jonthomasson/retroii/retroii-case/Apple_II_europlus_side.jpg

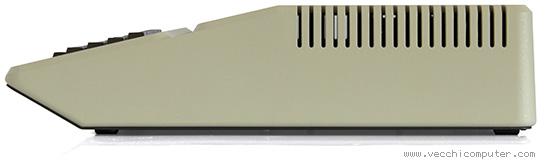
retroii-case/Apple_II_europlus_side.jpg
