jonthomasson/retroii/retroii-case/audio_cassette.png

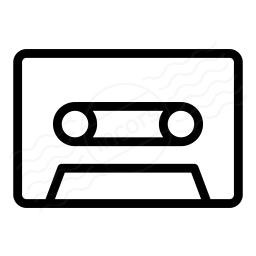
retroii-case/audio_cassette.png
