jonthomasson/retroii/retroii-case/choplft1.png

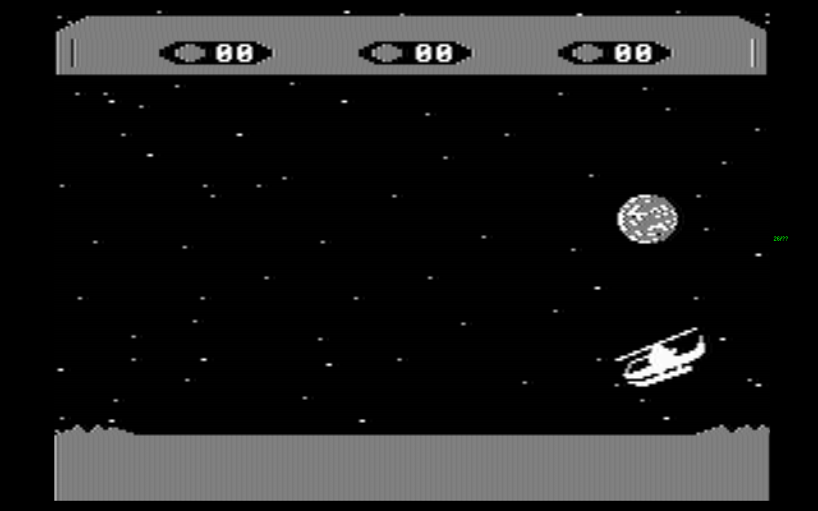
retroii-case/choplft1.png
