jonthomasson/retroii/retroii-case/headphones.png

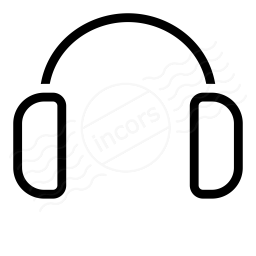
retroii-case/headphones.png
