jonthomasson/retroii/retroii-case/image81591.png

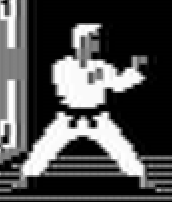
retroii-case/image81591.png
