jonthomasson/retroii/retroii-case/karateka.png

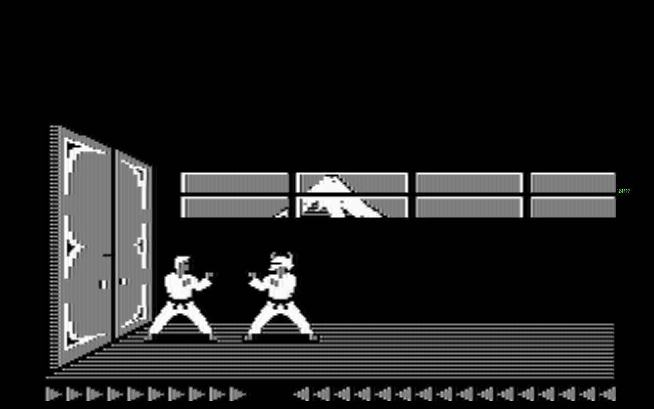
retroii-case/karateka.png
