jonthomasson/retroii/rev1.a/retroii/pics/kbd_latch.PNG

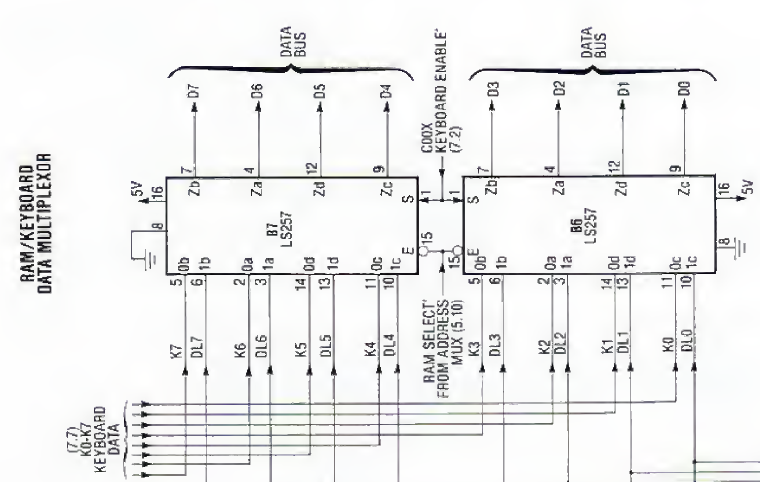
rev1.a/retroii/pics/kbd_latch.PNG
