jonthomasson/retroii/3d/D15S33E4GV00LFC.stp

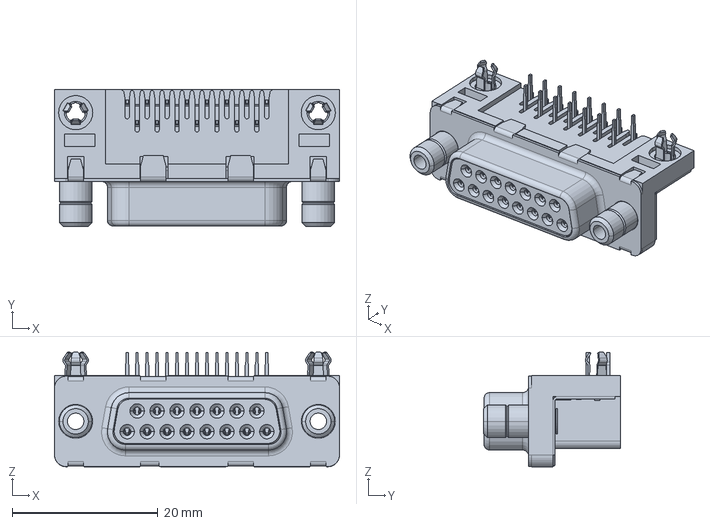
[picture p28: CAD file, 2019-04-12]
3d/D15S33E4GV00LFC.stp
39.1 x 18.8 x 15.8 mm
