jonthomasson/retroii/3d/CONN_5747844-6.step

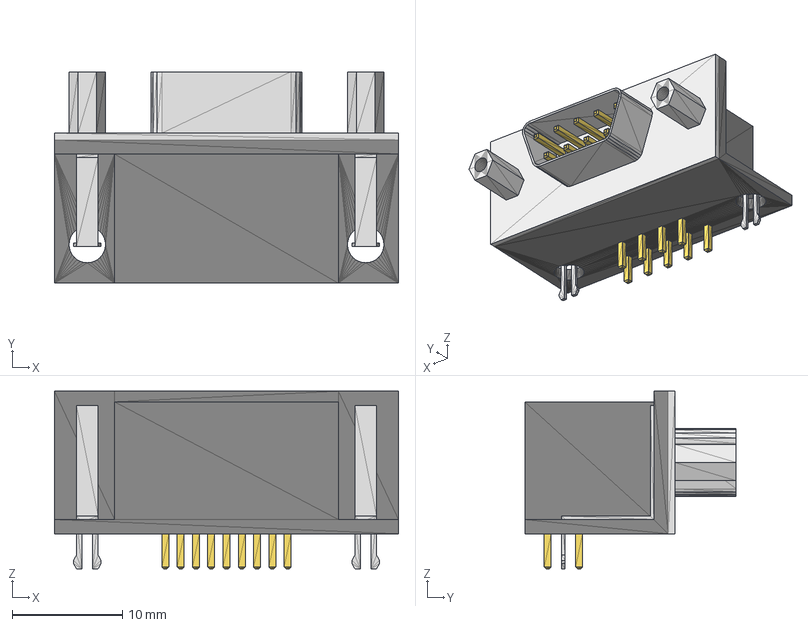
[picture p29: CAD file, 2019-04-12]
3d/CONN_5747844-6.step
31.2 x 19.2 x 16.1 mm
