jonthomasson/retroii/firmware/retroii/video/r2_video.spin

''------------------------------------------------------------------------------------------------
'' RETRO ][ video driver
''
'' Copyright (c) 2020 Jon Thomasson
''
''------------------------------------------------------------------------------------------------

'' This version uses two cogs, one for the VGA output, and one for routines that draw
'' on the bitmap.
''------------------------------------------------------------------------------------------------
'' Video Circuit:
''
'' Pin              VGA
'' Group   240Ω
''  +0 ──────── 14 Vertical Sync                +5V ──── 9
''         240Ω
''  +1 ──────── 13 Horizontal Sync              GND ┳─── 5
''         470Ω                                          │
''  +2 ──────┳─ 3  Blue                              ┣─── 6
''         240Ω │                                        │
''  +3 ──────┘                                        ┣─── 7
''         470Ω                                          │
''  +4 ──────┳─ 2  Green                             ┣─── 8
''         240Ω │                                        │
''  +5 ──────┘                                        └─── 10
''         470Ω                                         
''  +6 ──────┳─ 1  Red
''         240Ω │
''  +7 ──────┘
''------------------------------------------------------------------------------------------------

CON

  '288x240 resolution
  WIDTH  = 288 '288
  HEIGHT = 240
  FREQ_VALUE = 608207634 '304103817 '304104364
  CTRA_VALUE = %0_00001_011 '%0_00001_100
  FP = 7 '7
  SP = 43'43
  BP = 22'22

  'Color value constants
  #$04, BLUE, #$08, GREEN
  #$10, RED, #$0C, LT_BLUE
  #$18, YELLOW, #$14, LT_RED
  #$00, BLACK, #$1C, WHITE 
  #$FF, FULL 'full 6 color pallet mode

  PC_FP  = WIDTH + FP
  BLKS   = 480 / HEIGHT         'Number of times to repeat each video line

  COLS   = WIDTH / 8            'Width of screen in characters
  ROWS   = HEIGHT / 8           'Height of screen in characters
  MAX_C  = COLS - 1             'Maximum column
  MAX_R  = ROWS - 1             'Maximum row

  PSIZE  = WIDTH * HEIGHT       'Total number of pixels
  LSIZE  = PSIZE / 32           'Size of screen buffer in longs
  LPROW  = 10 'COLS / 4             'Longs per screen line

  MAX_X  = WIDTH - 1            'Maximum value of x coordinate
  MAX_Y  = HEIGHT - 1           'Maximum value of y coordinate

  SCROFF = WIDTH                'Scroll offset
  SCRCNT = LSIZE - (SCROFF / 4) 'Scroll long count

  CMD_CHAR  = $00_00_00_00
  CMD_PIXEL = $04_00_00_00
  CMD_LORES = $10_00_00_00
  CMD_HIRES  = $20_00_00_00
  
  MODE_HIRES = 2
  MODE_TEXT = 1
  MODE_LORES = 3
  
  LBUFFER_SIZE = 2400           'Size of pixel buffer in longs (320*240/32) NOTE: this size accounts for the color bit.
  BUFFER_WIDTH = 320
  
VAR 
  byte  cursorx, cursory, cog1, cog2, cog3, reverse, cursor_state, mode_retroii, mode_retroii_old, ss_page2, ss_mix, update_vcfg, screen_mode, old_screen_mode
  long  pixel_bfr[LBUFFER_SIZE]
  long  pixel_colors, frame_count, cursor_pos, cursor_mask, hires_busy, draw_command, hires_command, debug_val, display_debug, current_clock
  long  frame_count_hires', ram_lock                        
  'long  group1_colors, group2_colors 'color paletts. 

PUB Char(c) | idx, ptr, tmp
'------------------------------------------------------------------------------------------------
'' Print a character on the screen, then advance the cursor.
''
'' c - Character to print.
'------------------------------------------------------------------------------------------------
  c &= 255
  
  'If a printable character
  if c > 31
    repeat while draw_command <> 0
    draw_command := c | (cursorx << 8) | (cursory << 17)
    cursorx += 1
 
  'UpdateCursor

PUB RChar(c)
'------------------------------------------------------------------------------------------------
'' Print a character on the screen, in reverse video, then advance the cursor.
''
'' c - Character to print.
'------------------------------------------------------------------------------------------------
  reverse := 255
  Char(c)
  reverse := 0

PUB LowRes(c, x, y) 
'------------------------------------------------------------------------------------------------
'' Plots a lores byte of data on the screen.
''
'' c - data byte.
'' x - The X coordinate.
'' y - The Y coordinate.
'------------------------------------------------------------------------------------------------
  repeat while draw_command <> 0
  draw_command := c | (x << 8) | (y << 17) | CMD_LORES


PUB Str(s) | b
'------------------------------------------------------------------------------------------------
'' Write a NULL terminated string starting at the current cursor position.
''
'' s - Address of a Null terminated string.
'------------------------------------------------------------------------------------------------
  repeat
    b := byte[s]
    if b == 0
      return
    Char(b)
    s += 1

PUB Pos(X, Y)
'------------------------------------------------------------------------------------------------
'' Set the XY position of the character cursor.
'------------------------------------------------------------------------------------------------
  cursorx := X
  cursory := Y
  'cursorx := (X <# MAX_C) #> 0 
  'cursory := (Y <# MAX_R) #> 0 
  'UpdateCursor

PUB GetX
'------------------------------------------------------------------------------------------------
'' Returns the x cursor coordinate.
'------------------------------------------------------------------------------------------------
  return cursorx

PUB GetY
'------------------------------------------------------------------------------------------------
'' Returns the y cursor coordinate.
'------------------------------------------------------------------------------------------------
  return cursory

PUB Cursor(state)
'------------------------------------------------------------------------------------------------
'' Sets the cursor state.
''
'' state - True to turn cursor on. Default is off.
'------------------------------------------------------------------------------------------------
  cursor_state := state
  cursor_mask := 0
  'UpdateCursor

PUB Clear(first_line, line_count)
'------------------------------------------------------------------------------------------------
'' Clear a number of scan lines in the pixel buffer.
''
'' first_line - The first scan line to clear.
'' line_count - The number of scan lines to clear.
'------------------------------------------------------------------------------------------------
  first_line := (first_line <# MAX_Y) #> 0 
  line_count := (line_count <# HEIGHT) #> 0 

  longfill(@pixel_bfr + (COLS * first_line), 0, line_count * LPROW)

PUB ClearScreen
    longfill(@pixel_bfr, 0, LBUFFER_SIZE)
    
PUB Pixel(c, x, y) | p
'------------------------------------------------------------------------------------------------
'' Plots a byte of pixels on the screen.
''
'' c - byte containing pixel data.
'' x - The X pixel coordinate.
'' y - The Y pixel coordinate.
'------------------------------------------------------------------------------------------------
  repeat while draw_command <> 0
  draw_command := c | (x << 8) | (y << 17) | CMD_PIXEL

PUB PixelByte(data, col, row) | p, mask, data2, x
'------------------------------------------------------------------------------------------------
'' Plots a byte of pixels on the screen.
''
'' c - byte containing pixel data.
'' x - The X pixel coordinate.
'' y - The Y pixel coordinate.
'------------------------------------------------------------------------------------------------
  
  data &= $7F 'get rid of msb
  x := (col * 7) '- 7
  p := (WIDTH * row) + x 'get byte location of our column of data
  
  'x := |<(p & 7) 'finds x coord in byte
  x := (p & 7) 'find x position in byte
  
  p := @pixel_bfr + (p >> 3) ' find our byte inside the pixel buffer
  data2 := data << (x)
  mask := $FF000080 <- x
  byte[p] &= mask
  'write data to 1st byte
  byte[p] |= data2
  'return data2
  if x > 1
    data2 := data >> (8 - x) 'data for right most byte
    mask := $FF << (x - 1)
    byte[p + 1] &= mask
    byte[p + 1] |= data2

PUB HiRes
    repeat while hires_command <> 0
    hires_command := CMD_HIRES
   
   
      
PUB Line(c, x1, y1, x2, y2)' | dx, dy, df, a, b, d1, d2
'------------------------------------------------------------------------------------------------
'' Draw a line on the screen.
''
'' c      - Color number, 0 or 1.
'' x1, y1 - XY coordinates of start of line.
'' x2, y2 - XY coordinates of end of line.
'------------------------------------------------------------------------------------------------
  'repeat while draw_command <> 0
  'draw_command := c | (x1 << 8) | (y1 << 17) | CMD_START
  'repeat while draw_command <> 0
  'draw_command := c | (x2 << 8) | (y2 << 17) | CMD_HIRES

  
PUB LineTo(c, x, y)
'------------------------------------------------------------------------------------------------
'' Draw a line on the screen starting from the end of the last line.
''
'' c    - Color number, 0 or 1.
'' x, y - XY coordinates of end of line.
'------------------------------------------------------------------------------------------------
  repeat while draw_command <> 0
  draw_command := c | (x << 8) | (y << 17) | CMD_HIRES

PUB FrameCount
'------------------------------------------------------------------------------------------------
'' Returns the current frame counter.
'' Frame counter is incremented after the last video line is output.
'' Frame counter is an 32 bit integer.
'------------------------------------------------------------------------------------------------
  return frame_count

PUB FrameCountHires
    return frame_count_hires
    
PUB ClearFrameCountHires
    frame_count_hires := 0

PUB Color(color_num, new_color)
'------------------------------------------------------------------------------------------------
'' Change a color value.
''
'' color_num - The color number to change for the whole screen, 0 or 1.
'' new_color - A color byte (%RR_GG_BB_xx) describing the pixel's new color.
'------------------------------------------------------------------------------------------------
  if(new_color) == $FF 'if full color mode
    'need to set vcfg for 4 color mode
    screen_mode := $FF 'rgb color monitor
    vcfg_reg := $30_00_04_1F 'set for 4 color mode vga    
    update_vcfg := $FF 'tell vga driver to update vcfg                   
  else  'monochrome
    screen_mode := $00 'monochrome monitor
    'set vcfg to 2 color mode
    if old_screen_mode <> screen_mode 'going from color to monochrome, update vcfg
        vcfg_reg := $20_00_04_1F 'set for 2 color mode vga                                   
        update_vcfg := $FF 'tell vga driver to update vcfg    
    color_num &= 1
    pixel_colors.byte[color_num] := new_color
  
  old_screen_mode := screen_mode
                                      

PUB Start(pin_group) | hres, vres
'------------------------------------------------------------------------------------------------
'' Starts up the RetroII driver running on a cog.
'' Returns true on success and false on failure.
''
'' pin_group - Pin group to use to drive the video circuit. Between 0 and 3.
'------------------------------------------------------------------------------------------------
  Stop

  pin_group &= 3
  output_enables := ($FF << (pin_group << 3))
  vcfg_reg := $20_00_04_1F 'set for 2 color mode vga   '$20_00_04_1F '| (pin_group << 9)
  update_vcfg := $00
  screen_mode := $00 'monochrome
  update_vcfg_ptr := @update_vcfg
  screen_mode_ptr := @screen_mode
  hires_screen_mode_ptr := @screen_mode
  draw_screen_mode_ptr := @screen_mode
     
  colors_ptr := @pixel_colors
  
  frame_cntr_ptr := @frame_count
  frame_count_hires := 0
  frame_cnt_hres_ptr := @frame_count_hires 
  cursorx := 0
  cursory := 0
  cursor_state := FALSE
  cursor_pos := 0
  cursor_pos_ptr := @cursor_pos
  cursor_mask := 0
  cursor_mask_ptr := @cursor_mask
  reverse := 0
  draw_command := 0
  hires_command := 0
  hires_busy := 0
  hires_busy_ptr := @hires_busy
  debug_val_ptr := @debug_val
  mode_retroii_ptr := @mode_retroii 
  ss_page2_ptr := @ss_page2
  ss_mix_ptr := @ss_mix
  cog1 := cognew(@asm_start, @pixel_bfr) + 1
  if cog1 == 0
    return FALSE

  draw_cmnd_ptr := @draw_command
  draw_cmnd_ptr2 := @draw_command
  hires_cmnd_ptr := @hires_command
  draw_map_ptr := @AppleIICharMap
  draw_map_ptr2 := @AppleII3PixelFont
  'draw_graphmap_ptr := @FontToGraphicMap
  draw_reverse_ptr := @reverse
  
  draw_ymulwidth_ptr := @YMulWidth
  hires_ymulwidth_ptr := @YMulWidth
  hires_odd_lut_ptr := @ColorOdd
  hires_oddc_lut_ptr := @ColorOddC
  hires_even_lut_ptr := @ColorEven
  hires_evenc_lut_ptr := @ColorEvenC
  hires_blank_lut_ptr := @ColorBlankTest
  hires_default_lut_ptr := @ColorDefaultTest
  
  cog2 := cognew(@draw_start, @pixel_bfr) + 1
  if cog2 == 0
    cogstop(cog1 - 1)
    return FALSE  
    
  cog3 := cognew(@hires_cmd_start, @pixel_bfr) + 1
  if cog3 == 0
    return FALSE  

  return TRUE  
  
PUB DebugOutput
    return debug_val

PUB Stop
'------------------------------------------------------------------------------------------------
'' Shuts down the RetroII driver running on a cog.
'------------------------------------------------------------------------------------------------
  if cog1 > 0
    cogstop(cog1 - 1)

  if cog2 > 0
    cogstop(cog2 - 1)
'------------------------------------------------------------------------------------------------
''Set registers for current mode, soft switches, debug display, and clock speed
'------------------------------------------------------------------------------------------------
PUB UpdateRegs(page2, mix, debug, clock)
    'mode_retroii := mode
    ss_page2 := page2
    ss_mix := mix 
    display_debug := debug
    current_clock := clock

PUB UpdateRetroIIMode(mode)
    
    mode_retroii := mode
    'check with old mode to see if we're going from hires to something else
    if mode_retroii_old <> mode_retroii 'new mode
    'while loop that waits for hires to stop?
        if mode_retroii_old == MODE_HIRES
            repeat while hires_busy == 1    'if switching from hires, need to wait till hires is done running
    
    mode_retroii_old := mode_retroii
            
        
'PRI UpdateCursor | cpos, cx, offset, x
'------------------------------------------------------------------------------------------------
'' Update the cursor position.
'------------------------------------------------------------------------------------------------
  
  'if cursor_state
  '  x := cursorx * 2
  '  cx := byte[@FontToGraphicMap][x]
  '  offset := byte[@FontToGraphicMap][x + 1]
    
  '  cpos := @pixel_bfr + (cursory * WIDTH) + constant(7 * COLS) 'need to get rid of cols
  '  cpos := cpos + (cx & $FFFC)
  '  if offset > 0
  '      cursor_mask := $FE << ((cx & 3) << 3) << (6 - offset)
  '  else
  '      cursor_mask := $FE << ((cx & 3) << 3) '>> (offset)
    'ptr := @pixel_bfr + (graphicx + (cursory * WIDTH))
  '  cursor_pos := cpos

DAT
'------------------------------------------------------------------------------------------------
                        org     0

asm_start               mov     frqa, freq_reg
                        movi    ctra, #CTRA_VALUE
                        mov     vcfg, vcfg_reg
                        mov     dira, output_enables
{
Timing taken from :http://tinyvga.com/vga-timing/640x480@60Hz

                    640 X 480 VIDEO TIMING 
                            HSYNC
         ____________________________________________ _____16______ _____96_____ _____48____
         |                 DISPLAY                   | FRONT PORCH | SYNC PULSE | BACK PORCH|
         |                                           |
         |                                           |
         |                                           |
         |                                           |
         |                                           |
      V  |                                           |
      S  |                                           |
      Y  |                                           |
      N  |                                           |
      C  |                                           |
         |                                           |      
         |                                           |      
         |___________________________________________|                                                
         |
         |
         |10 FRONT PORCH
         |
         |-
         |
         |2 SYNC PULSE
         |                                      BLANKING AREA
         |-
         |
         |33 BACK PORCH
         |
         |_
         
GENERAL TIMING
    -SCREEN REFRESH RATE:   60HZ
    -VERTICAL REFRESH:      31.46875KHZ
    -PIXEL FREQ:            25.175MHZ
    
HORIZONTAL TIMING
| SCANLINE PART | PIXELS | TIME uS 
| VISIBLE AREA  | 640    | 25.422045680238
| FRONT PORCH   | 16     | 0.63555114200596
| SYNC PULSE    | 96     | 3.8133068520357
| BACK PORCH    | 48     | 1.9066534260179
| WHOLE LINE    | 800    | 31.777557100298

VERTICAL TIMING
| SCANLINE PART | PIXELS | TIME uS 
| VISIBLE AREA  | 480    | 15.253227408143
| FRONT PORCH   | 10     | 0.31777557100298
| SYNC PULSE    | 2      | 0.063555114200596
| BACK PORCH    | 33     | 1.0486593843098
| WHOLE FRAME   | 525    | 16.683217477656


below are the routines for the VGA driver. They consist of 4 main loops.
These loops drive the vertical sync pulse (vsync_loop), the vertical sync
back porch (vsbp_loop), the active video lines (video_loop1), and finally
the vertical sync front porch (vsfp_loop). These loops provide the video signals
for the VGA and are repeated indefinitely.
}

'--- Vertical Sync ------------------------------------------------------------------------------
vsync_loop              mov     line_cntr, #2                       'sync pulse is 2 lines for 640x480 spec

vs_loop                 mov     vscl, #PC_FP
                        waitvid vs_colors, #0
                        mov     vscl, #SP
                        waitvid vs_colors, #1
                        mov     vscl, #BP
                        waitvid vs_colors, #0
                        djnz    line_cntr, #vs_loop

'--- Vertical Sync Back Porch -------------------------------------------------------------------
                        mov     line_cntr, #33                      'back porch is 33 lines

vsbp_loop               mov     vscl, #PC_FP
                        waitvid hs_colors, #0
                        mov     vscl, #SP
                        waitvid hs_colors, #1
                        mov     vscl, #BP
                        waitvid hs_colors, #0
                        djnz    line_cntr, #vsbp_loop

'--- Prep for Active Video ----------------------------------------------------------------------
                        mov     vscl, #PC_FP

                        mov     pixel_ptr0, par
                        
                        mov     line_cntr, #HEIGHT                  'active video lines = resolution height
                        rdlong  vid_mono_color, colors_ptr
                        or      vid_mono_color, blank_colors
                       
                        'mov     cursor_mask0, frame_cntr            'mask off cursor, if cursor is in visible area?
                        'and     cursor_mask0, #$20  wz
              'if_nz     mov     cursor_mask0, #0
              'if_z      rdlong  cursor_mask0, cursor_mask_ptr
                        'rdlong  cursor_pos0, cursor_pos_ptr

                        waitvid hs_colors, #0
                        mov     vscl, #SP
                        waitvid hs_colors, #1
                        mov     vscl, #BP
                        waitvid hs_colors, #0

'--- Active Video Lines -------------------------------------------------------------------------
video_loop1             mov     block_cntr, #BLKS                   'will repeat each video line twice (480/240 height)
video_loop2             'mov     vscl, video_scale                   'video_scale is $000_01_020
                        'mov     pixel_cntr, #LPROW
                        'mov     pixel_ptr1, pixel_ptr0
                        
'video_loop3             rdlong  pixel_values, pixel_ptr1            'main loop to display pixel buffer for a single line
              '          cmp     pixel_ptr1, cursor_pos0  wz
              'if_z      or      pixel_values, cursor_mask0
                        '1 long has 14 color or 28 monochrome pixels
                        '1 long has 4 color bits
                        'need to shift out color bits
                        '10 longs times 28 pixels per long = 280 resolution
                        'active video pixels should be 288 for our driver
                        
                        mov     pixel_cntr,#20                  '40 columns/2 bytes per word
                        
                        mov     pixel_ptr1, pixel_ptr0
                        
        
                        rdbyte  tmp1, screen_mode_ptr  wz       'check screen mode
        if_z            jmp     #video_loop_monochrome          'if zero then monochrome
        if_nz           jmp     #video_loop_color               'else color
              
video_loop_color        rdword  pixel_values,pixel_ptr1
                        add     pixel_ptr1,#2
                        
                        'odd byte
                        'test color write to z flag
                        test    pixel_values, bit8 wz           'if zero then group 1 else group 2
        if_z            mov     vid_colors, group1_vid_colors
        if_nz           mov     vid_colors, group2_vid_colors
                        mov     vscl,vscl_3pixel
                        waitvid vid_colors,pixel_values         'display 3 pixels of odd byte
                        
                        'even byte
                        test    pixel_values, bit7 wc           'move bit 7 from odd byte up so we can display it with even byte
                        muxc    pixel_values, bit8
                        test    pixel_values, bit15 wz          'if zero then group 1 else group 2
        if_z            mov     vid_colors, group1_vid_colors
        if_nz           mov     vid_colors, group2_vid_colors
                        shr     pixel_values,#7                 'shift out first 3.5 pixels
                        mov     vscl,vscl_4pixel
                        waitvid vid_colors,pixel_values         'display 4 pixels of even byte
                        djnz    pixel_cntr,#video_loop_color
                        jmp     #video_loop3 

video_loop_monochrome   mov     vscl, vscl_7pixel

video_loop_monochrome2  rdword  pixel_values,pixel_ptr1
                        add     pixel_ptr1,#2
                        
                        waitvid vid_mono_color, pixel_values
                        
                        shr     pixel_values, #8
                        waitvid vid_mono_color, pixel_values
                       
                        djnz    pixel_cntr, #video_loop_monochrome2
                        
                        
video_loop3                       
                        'buffer 8 pixels around our 280 to get 288
                        mov     vscl, vscl_8pixel
                        waitvid vid_mono_color, #0
                        
                        
                        mov     vscl, #FP
                        waitvid hs_colors, #0
                        mov     vscl, #SP
                        waitvid hs_colors, #1
                        mov     vscl, #BP
                        waitvid hs_colors, #0

                        djnz    block_cntr, #video_loop2
                        add     pixel_ptr0, #40 '#COLS
                        djnz    line_cntr, #video_loop1

'----Vertical Sync Front Porch ------------------------------------------------------------------
                        mov     line_cntr, #10                      'front porch is 10 lines
                        add     frame_cntr, #1
                        wrlong  frame_cntr, frame_cntr_ptr 

vsfp_loop               mov     vscl, #PC_FP
                        waitvid hs_colors, #0
                        mov     vscl, #SP
                        waitvid hs_colors, #1
                        mov     vscl, #BP
                        waitvid hs_colors, #0
                        djnz    line_cntr, #vsfp_loop

                        'check to see if we need to load a new vcfg for 2 or 4 color video
                        rdbyte  tmp1, update_vcfg_ptr  wz       
        if_z            jmp     #vsync_loop                         'no updates, continue
                        rdbyte  tmp1, screen_mode_ptr  wz
        if_z            mov     vcfg, vcfg_2color                   'else update vcfg
        if_nz           mov     vcfg, vcfg_4color                            
                                             
                        mov     tmp1, #0
                        wrbyte  tmp1, update_vcfg_ptr               'reset update pointer
                        jmp     #vsync_loop

group1_vid_colors       long    $1F_0B_17_03 'white/green/magenta/black
group2_vid_colors       long    $1F_13_0F_03 'white/red(orange)/blue/black
hs_colors               long    $01_03_01_03
vs_colors               long    $00_02_00_02
blank_colors            long    $03_03_03_03
vcfg_4color             long    $30_00_04_1F
vcfg_2color             long    $20_00_04_1F
colors_ptr              long    0
screen_mode_ptr         long    0
update_vcfg_ptr         long    0
cursor_pos_ptr          long    0
cursor_mask_ptr         long    0
freq_reg                long    FREQ_VALUE
vcfg_reg                long    0
output_enables          long    0
frame_cntr_ptr          long    0
video_scale             long    $000_01_010
vscl_4pixel             long    $000_02_008
vscl_3pixel             long    $000_02_006
vscl_6pixel             long    $000_01_006
vscl_7pixel             long    $000_01_007
vscl_8pixel             long    $000_01_008
vscl_14pixel            long    $000_01_00E
vscl_280pixel           long    $000_01_118
bit32                   long    $80_00_00_00
bit25                   long    $01_00_00_00
bit24                   long    $00_80_00_00
bit15                   long    $00_00_80_00
bit14                   long    $00_00_40_00
bit9                    long    $00_00_01_00
bit8                    long    $00_00_00_80
bit7                    long    $00_00_00_40
tmp1                    long    0

vid_colors              res     1
vid_mono_color          res     1
pixel_ptr0              res     1
pixel_ptr1              res     1
pixel_cntr              res     1
pixel_cntr2             res     1
pixel_values            res     1
current_pixels          res     1
line_cntr               res     1
block_cntr              res     1
frame_cntr              res     1
cursor_pos0             res     1
cursor_mask0            res     1
                        fit

'------------------------------------------------------------------------------------------------
' Routines to draw on the bitmap
'------------------------------------------------------------------------------------------------
                        org     0

'---- Wait for a command, then decode -----------------------------------------------------------
draw_start              rdlong  draw_cmnd, draw_cmnd_ptr  wz
              if_z      jmp     #draw_start

                        rdbyte  draw_screen_mode, draw_screen_mode_ptr 'color vs monochrome screen
                        
                        mov     draw_cntr, #0
                        wrlong  draw_cntr, draw_cmnd_ptr 'reset draw_command to 0 accept new command

                        mov     draw_val, draw_cmnd
                        and     draw_val, #255
                        shr     draw_cmnd, #8
                        mov     draw_xpos, draw_cmnd
                        and     draw_xpos, #511
                        shr     draw_cmnd, #9
                        mov     draw_ypos, draw_cmnd
                        and     draw_ypos, #511
                        shr     draw_cmnd, #9

                        'cmp     draw_cmnd, #8  wz
              'if_z      jmp     #draw_hires

                        'cmp     draw_cmnd, #1  wz
              'if_z      jmp     #draw_pixel

                        cmp     draw_cmnd, #4  wz
              if_z      jmp     #draw_lores
            
'---- Draw a character --------------------------------------------------------------------------
'    c := (c - 32) << 3
draw_char               test    draw_screen_mode, #1  wc       'check screen mode
                        rdbyte  draw_reverse, draw_reverse_ptr
                        sub     draw_val, #32
                        shl     draw_val, #3
              if_nc     mov     draw_ptr1, draw_map_ptr     'monochrome font
              if_c      mov     draw_ptr1, draw_map_ptr2    'color mode 3 pixel white font.
                        add     draw_ptr1, draw_val
                        
'    'need to determine which 8x8 graphic tile(s) we need to update
'    x := cursorx * 2
                        mov     draw_x, draw_xpos                       'copy xpos to x
                        'shl     draw_x, #1                              'shift left one time to mult by 2

'    graphicx := byte[@FontToGraphicMap][x] 'graphic tile column
                        'mov     char_t1, draw_graphmap_ptr
                        'add     char_t1, draw_x  
                        'rdbyte  char_graphicx, char_t1  
                 
'    offset := byte[@FontToGraphicMap][x + 1] 'offset for our font tile
                        'add     char_t1, #1
                        'rdbyte  char_offset, char_t1
                        
'    ptr := @pixel_bfr + (graphicx + (cursory * WIDTH))
                        mov     draw_ptr0, #0                           '0 out pointer
draw_char1              test    draw_ypos, #255  wz                     'mult cursory * width

                         
                        
              if_nz     sub     draw_ypos, #1               
              if_nz     add     draw_ptr0, #BUFFER_WIDTH
              if_nz     jmp     #draw_char1

                        
                        
                        add     draw_ptr0, draw_x 'char_graphicx                'add graphicx
                        add     draw_ptr0, par                          'add @pixel_bfr
                        
'    repeat idx from 0 to 7 'y
                        mov     draw_cntr, #8
                                             
'        tmp := byte[@C64CharMap][idx + c] 'pointer to our char in font rom
draw_char3              rdbyte  draw_xpos, draw_ptr1
                        add     draw_ptr1, #1        
                        

                        mov     char_t1, #255
                        shl     char_t1, #7

                        rdbyte  char_ptr0, draw_ptr0
                        and     char_ptr0, char_t1
                        
                        'if in color mode, shift byte over and or it with itself to display white text
                        'cmp     draw_screen_mode, #0  wz       'check screen mode
              'if_nz     mov     char_t2, draw_xpos
              'if_nz     shr     char_t2, #1
              'if_nz     or      draw_xpos, char_t2 
              
              'send byte to hires lut
              
                        'if in color mode and even byte , shift bits over 1 to align with white pallet.
            if_c        test    draw_x, #1  wz
            if_nz_and_c shr     draw_xpos, #1      'nz even 
            'if_z_and_c  test    draw_x, #2  wz     '2nd odd
            'if_z_and_c  rol     draw_xpos, #2      'odd rotate spaces to other side
            'if_nz_and_c shr     draw_xpos, #1
            'if_z_and_c  shr     draw_xpos, #1
            
                        xor     draw_xpos, draw_reverse
                       
                        or      char_ptr0, draw_xpos
                        wrbyte  char_ptr0, draw_ptr0                       
                        jmp     #draw_char5
                        


'        ptr += COLS 'increment ptr to go to next y coord of graphic tile
draw_char5              add     draw_ptr0, #40 '#COLS     
                        
                        djnz    draw_cntr, #draw_char3
                        jmp     #draw_start                                 


'---- draw a byte of lores mode ------------------------------------------------
draw_lores       
    'bottom block = left nibble
    'bottom := data >> 4
    'bottom |= (data & $F0) 'duplicate nibble on both s
    'bottom &= $0FE
                        mov     draw_tmp, draw_val
                        shr     draw_tmp, #4
                        mov     lores_bottom, draw_tmp
                        mov     draw_tmp, draw_val
                        and     draw_tmp, #240
                        or      lores_bottom, draw_tmp
                        and     lores_bottom, #254
    'top block = right nibble
    'top := data << 4
    'top |= (data & $0F) 'duplicate nibble on both sides
    'top &= $0FE
                        mov     draw_tmp, draw_val
                        shl     draw_tmp, #4
                        mov     lores_top, draw_tmp
                        mov     draw_tmp, draw_val
                        and     draw_tmp, #15
                        or      lores_top, draw_tmp  
                        and     lores_top, #254   
    'need to determine which 8x8 graphic tile(s) we need to update
    'x := x << 1 'x * 2
                        mov     draw_x, draw_xpos                       'copy xpos to x
                        'shl     draw_x, #1                              'shift left one time to mult by 2

    'graphicx := byte[@FontToGraphicMap][x] 'graphic tile column
                        'mov     char_t1, draw_graphmap_ptr
                        'add     char_t1, draw_x  
                        'rdbyte  char_graphicx, char_t1  
                 
    'offset := byte[@FontToGraphicMap][x + 1] 'offset for our font tile
                        'add     char_t1, #1
                        'rdbyte  char_offset, char_t1
                        
    'ptr := @pixel_bfr + (graphicx + (Y * WIDTH))
                        mov     draw_ptr0, #0                           '0 out pointer
draw_lores1             test    draw_ypos, #255  wz                     'mult cursory * width

                         
                        
              if_nz     sub     draw_ypos, #1               
              if_nz     add     draw_ptr0, #BUFFER_WIDTH
              if_nz     jmp     #draw_lores1

                        
                        'new routine using lut to replace multiply
                        'rdlong would be more efficient here, but 
                        'there was a problem reading bytes since they weren't
                        'long aligned...
                        'mov     char_t1, draw_ymulwidth_ptr
                        'shl     draw_ypos, #1
                        'add     char_t1, draw_ypos  
                        'rdbyte  draw_ptr0, char_t1 
                        'add     char_t1, #1
                        'shl     draw_ptr0, #8
                        'rdbyte  char_t2, char_t1 
                        'or      draw_ptr0, char_t2
                        
                        'start debug
                        'mov     debug_ptr, draw_ypos
                        'wrlong  debug_ptr, debug_val_ptr
                        'jmp     #draw_start  
                        'end debug
                        
                        add     draw_ptr0, draw_x 'char_graphicx                'add graphicx
                        add     draw_ptr0, par                          'add @pixel_bfr
    'ptr2 := ptr + 1 '@pixel_bfr + ((graphicx + 1) + (cursory * WIDTH))
                        'mov     draw_ptr2, draw_ptr0
                        'add     draw_ptr2, #1
                        
'    repeat idx from 0 to 7 'y
                        mov     draw_cntr, #8
                        'mov     char_offset2, char_offset
                        'add     char_offset2, #1                        
    '    if idx < 4
    '        tmp := top
    '    else
    '        tmp := bottom
draw_lores3             
                        cmp     draw_cntr, #5  wc
              if_nc     mov     draw_xpos, lores_top
              if_c      mov     draw_xpos, lores_bottom
              
                        'tjnz    char_offset, #draw_lores4    
                        'if offset is zero fall through to below code
'        else 'font tile is encapsulated in one graphic tile
'            byte[ptr] &= $FF << 7 'mask to clear offset bits
'            byte[ptr] |= (tmp) >> (offset + 1)

                        mov     char_t1, #255
                        shl     char_t1, #7

                        rdbyte  char_ptr0, draw_ptr0
                        and     char_ptr0, char_t1
                        
                        'shr     draw_xpos, char_offset2
                        
                        or      char_ptr0, draw_xpos
                        wrbyte  char_ptr0, draw_ptr0                       
                        jmp     #draw_lores5
                        
'       if offset > 0 '7x8 font tile will take up 2 graphic tiles                  

'            byte[ptr] &= !($FF << (8 - offset)) 'mask to clear offset bits
'            byte[ptr] |= (tmp) << (7 - offset) 'write left part of char
'draw_lores4             mov     char_t1, #8
                        'sub     char_t1, char_offset
                        'mov     char_t2, #255
                        'shl     char_t2, char_t1
                        'rdbyte  char_ptr0, draw_ptr0
                        'andn    char_ptr0, char_t2
                        
                        'mov     char_t2, draw_xpos 'make copy of draw_xpos so we can use it later
                        'mov     char_t1, #7
                        'sub     char_t1, char_offset
                        
                        'shl     draw_xpos, char_t1
                        
                        'or      char_ptr0, draw_xpos
                        'wrbyte  char_ptr0, draw_ptr0 
                         
'            byte[ptr2] &= !($FF >> (offset + 1)) 'mask
'            byte[ptr2] |= (tmp) >> (offset + 1)'right part of char
                        'mov     char_t1, #255
                        'shr     char_t1, char_offset2
                        'rdbyte  char_ptr0, draw_ptr2
                        'andn    char_ptr0, char_t1
                                
                        'xor     char_t2, draw_reverse
                        'shr     char_t2, char_offset2
                        
                        'or      char_ptr0, char_t2
                        'wrbyte  char_ptr0, draw_ptr2   
'            ptr2 += COLS 
                        'add     draw_ptr2, #COLS


'        ptr += COLS 'increment ptr to go to next y coord of graphic tile
draw_lores5             add     draw_ptr0, #40  '#COLS     
                        
                        djnz    draw_cntr, #draw_lores3
                        jmp     #draw_start          




draw_cmnd_ptr           long    0
draw_map_ptr            long    0
draw_map_ptr2           long    0
'draw_graphmap_ptr       long    0
draw_ymulwidth_ptr      long    0
draw_reverse_ptr        long    0
draw_lastx              long    0
draw_lasty              long    0
draw_screen_mode_ptr    long    0
draw_screen_mode        long    0

draw_cmnd               res     1
draw_val                res     1
draw_val2               res     1
draw_tmp                res     1
draw_tmp2               res     1
draw_xpos               res     1
draw_ypos               res     1
draw_x                  res     1
draw_ptr0               res     1
draw_ptr1               res     1
draw_ptr2               res     1
draw_cntr               res     1
draw_cntr2              res     1
draw_cntr3              res     1
draw_cntr4              res     1
draw_reverse            res     1
draw_a                  res     1
draw_b                  res     1
draw_x1                 res     1
draw_y1                 res     1
draw_x2                 res     1
draw_y2                 res     1
draw_dx                 res     1
draw_dy                 res     1
draw_d1                 res     1
draw_df                 res     1
char_graphicx           res     1
char_offset             res     1
char_offset2            res     1
char_t1                 res     1
char_t2                 res     1
char_ptr0               res     1
lores_bottom            res     1
lores_top               res     1

                        fit
'------------------------------------------------------------------------------------------------
' Routines to hires hires mode
'------------------------------------------------------------------------------------------------
                        org     0
'---- Wait for a command to start hires -----------------------------------------------------------
hires_cmd_start         rdlong  hires_cmnd, hires_cmnd_ptr  wz
              if_z      jmp     #hires_cmd_start

                        mov     hires_cntr, #0
                        wrlong  hires_cntr, hires_cmnd_ptr 'reset hires_command to 0 accept new command
                       
                        
                        wrlong  hires_is_busy, hires_busy_ptr 'hires is busy
			'jmp #hires
'---- draw HiRes screen--------------------------------------------------------------------------
hires_hires             'setup input/output for ram once
                        andn    dira, ram_dira_mask
                        or      dira, ram_dira_mask 'set proper input/outputs
                        or      outa, ram_we_mask                             
                        'mov     mode_retroii_ptr, #2 'in retroii mode
                        'mov     ram_address, ram_address_test
                        'call    #read_byte 
                        
                        'start debug
                        'mov     debug_ptr, ram_read
                        'wrlong  debug_ptr, debug_val_ptr
                        'jmp     #hires_start  
                        'end debug                        

'            mem_loc := HIRES_PAGE1    'set starting address  
'            mem_start := $00         
'            mem_page_start := HIRES_PAGE1
'            row := 0                          
hires_start             
                        rdbyte  hires_screen_mode, hires_screen_mode_ptr 'color vs monochrome screen
                        mov     mem_start, #0
                        mov     mem_page_start, hires_page1
                        mov     hires_row, hires_row_start
                        
'            if ss_page2 == $FF
'                mem_page_start := HIRES_PAGE2
                        rdbyte  hires_tmp, ss_page2_ptr wz
                        'xor     hires_tmp, #255 wz
                if_nz   mov     mem_page_start, hires_page2   
     
'            repeat mem_section from 1 to 3 '3 sections
                        mov     hires_cntr, #3  
hires_section  
'                mem_box := 0     
                        mov     hires_mem_box, #0
'                repeat 8 '8 box rows per section                             
                        mov     hires_cntr2, #8  
hires_boxrow          
            '        'mix mode
            '        if ss_mix == $FF
                        rdbyte  hires_tmp, ss_mix_ptr wz
                        'xor     hires_tmp, #255 wz
                if_z    jmp     #hires_start_row 'not in mixed mode, else fall through to below code                  
            '            'when we're at row 5 and section 3, exec mix mode
            '            'check mem_box and mem_start
            '            if mem_section == 3 and mem_box == $200
                        cmp     hires_cntr, #1  wz 'comparing 1 because we're counting down here, not up
                if_nz   jmp     #hires_start_row
                        cmp     hires_mem_box, mem_box_mix wz
                if_z    jmp     #mix_mode_start
            '                display_retroii_mixed(cursor_toggle)
            '                'jump out of loops
            '                mem_section := 3
            '                quit           
hires_start_row
'                    mem_row := 0
                        mov     hires_mem_row, #0   
'                    repeat 8 '8 rows within box row
                        mov     hires_cntr3, #8   
hires_draw_row
'                        mem_loc := mem_page_start + mem_start + mem_box + mem_row
                        mov     mem_loc, #0
                        add     mem_loc, mem_page_start
                        add     mem_loc, mem_start
                        add     mem_loc, hires_mem_box
                        add     mem_loc, hires_mem_row

                        mov     hires_ypos, hires_row 'pixel sub will iterate 1 row of pixels
                        call    #hires_pixel_sub       'call routine to draw our byte of pixels                                                                    

'                        row++
                        add     hires_row, #1
'                        mem_row += $400
                        add     hires_mem_row, mem_row_inc
                        djnz    hires_cntr3, #hires_draw_row
'                    mem_box += $80
                        add     hires_mem_box, #128
                        djnz    hires_cntr2, #hires_boxrow
'                mem_start += $28  
                        add     mem_start,#40   
                        djnz    hires_cntr, #hires_section wz
                       
                        'get updated value for mode_retroii
hires_check_mode        rdbyte  hires_tmp, mode_retroii_ptr
                        'update frame counter
                        rdlong  hires_val, frame_cnt_hres_ptr
                        add     hires_val, #1
                        wrlong  hires_val, frame_cnt_hres_ptr
                        
                        cmp     hires_tmp, #2  wz 'repeat loop while in retroii hires mode
              if_z      jmp     #hires_start
                        'start debug
                        'mov     debug_ptr, hires_tmp
                        'wrlong  debug_ptr, debug_val_ptr
                        'jmp     #hires_start  
                        'end debug
                        
                        
                        wrlong  hires_not_busy, hires_busy_ptr 'let other applications know we're not busy
                        jmp     #hires_cmd_start 'jump out of retroii mode and return control                        

mix_mode_start
'    mem_loc := $650
                        mov     mem_loc, mem_mix_start   
'    row := 20
                        mov     hires_mem_row, #20
'    repeat 4 '4 rows of text
                        mov     hires_cntr, #4
mix_mode_row  
'        display_retroii_textrow(row, mem_loc, cursor_toggle)
 '   col := 0
                        mov     hires_col, #0        
                        mov     hires_tmp2, mem_loc 'don't want to change mem_loc when iterating the columns
'    repeat 40 'columns
                        mov     hires_cntr2, #40
mix_mode_col
'        data := read_byte(mem_loc)
                        mov     ram_address, hires_tmp2
                        call    #read_byte
                        mov     hires_val, ram_read
'        flashing := false                       
                        mov     mix_flashing, #0
'        inverse := false                        
                        mov     mix_inverse, #0
'        type := $C0 & data                        
                        mov     hires_tmp, hires_val
                        and     hires_tmp, #192
'        if type == $40 'flashing text                        
                        cmp     hires_tmp, #64  wz 'flashing
              if_z      jmp     #mix_mode_flashing
'        elseif type == $00 'inverse
                        cmp     hires_tmp, #0   wz 'inverse
              if_z      jmp     #mix_mode_inverse
'        else
                        jmp     #mix_mode_normal   'else normal
mix_mode_flashing
'           flashing := true
                        mov     mix_flashing, #1
'           if data == $60 'cursor
'                        cmp     hires_val, #96  wz 'cursor
'                data := $DB
'              if_z      mov     hires_val, #219

'           else
'                if data > 95
                        cmp     hires_val, #96  wc,wz
'                    data -= $40
              if_nc     sub     hires_val, #64
              if_z      mov     hires_val, #219 'cursor
              
              'check flash_counter, if 0 then toggle is_flashing and reset counter
                        sub     flash_counter, #1 wz
              if_z      andn    is_flashing, is_flashing wz 'invert is_flashing
              if_z      mov     hires_val, #32 'space
              if_z      mov     flash_counter, #25 'reset counter          
                        'mov     hires_tmp, #0
                        'wrbyte  hires_tmp, draw_reverse_ptr2
                        jmp     #mix_mode_print
mix_mode_inverse
                        mov     mix_inverse, #1
'           if data < 32
                        cmp     hires_val, #32  wc
'                data += $40 
              if_c      add     hires_val, #64
              
              'set reverse ptr flag
                        'mov     hires_tmp, #255
                        'wrbyte  hires_tmp, draw_reverse_ptr2
                        'will need to rethink inverse, since setting this
                        'flag will also make any other calls to char set inverse.
                        'will possibly want to pass the inverse param through
                        'the draw command instead?...
                        jmp     #mix_mode_print
mix_mode_normal
                        'mov     hires_tmp, #0
                        'wrbyte  hires_tmp, draw_reverse_ptr2
'        data -= $80    
                        sub     hires_val, #128
mix_mode_print              
'        printxy(col, row,  data)                        
                        'ideally I could invoke the char method running on the other cog here.
'        c &= 255                        
                        and     hires_val, #255
    '    repeat while draw_command <> 0
    '        draw_command := c | (cursorx << 8) | (cursory << 17)
    '        'construct draw_command value first, then wait for draw_command to be available
                        mov     hires_tmp, hires_col
                        shl     hires_tmp, #8
                        or      hires_val, hires_tmp
                        mov     hires_tmp, hires_mem_row
                        shl     hires_tmp, #17
                        or      hires_val, hires_tmp
                        
mix_mode_wait           rdlong  hires_tmp, draw_cmnd_ptr2  wz 'wait for draw_command to be free
              if_nz     jmp     #mix_mode_wait
                        wrlong  hires_val, draw_cmnd_ptr2
'        col++
                        add     hires_col, #1
'        mem_loc++
                        add     hires_tmp2, #1
                        djnz    hires_cntr2, #mix_mode_col wz
'        row++
                        add     hires_mem_row, #1
'        mem_loc += $80                        
                        add     mem_loc, #128
                        djnz    hires_cntr, #mix_mode_row wz
                        jmp     #hires_check_mode

'reads a byte from RAM------------------------------------------------------------------
'ram_address should have the address you want to read from
'will place byte read into var ram_read
'this procedure won't affect the c flag
read_byte
                        'lock ram first to prevent other cogs from reading at same time
'read_byte_wait_lock     
'                        rdlong  hires_tmp, hires_ram_lock_ptr  wz 'wait for ram to be free
'              if_nz     jmp     #read_byte_wait_lock   
'                        wrlong  cog_num, hires_ram_lock_ptr 'lock ram with our unique cog number.      
'   'to read:   
'    lsb := address 
                        mov     ram_lsb, ram_address
                       
'    msb := address >> 8
                        shl     ram_address, #13
                        
'    'set we pin high
'    outa[WE]~~
                       
'    'set data pins as input
'    dira[D0..D7]~
                       
                        'updating dira to ram_dira_mask below        
'    'set address pins
'    outa[A7..A0] := lsb
                        shl     ram_lsb, #8 
                        and     ram_lsb, ram_lsb_mask  
                       
                       
'    outa[A14..A8] := msb
                        and     ram_address, ram_msb_mask     
                       
                        andn    outa, ram_mask
                        or      outa, ram_lsb
                        or      outa, ram_address
'    outa[A15] := msb >> 7
                       
'    'wait specified time
'    'can adjust the amount of nops here to optimize performance a bit
                        'nop
                        'nop
                        'nop
                        
'    'read data pins
'    data_in := ina[D7..D0]
                        mov     ram_read, ina
                        and     ram_read, #255 'clean the data
                        
'    outa[A0..A7] := %00000000 'lo
'    outa[A8..A14] := %0000000 'lo
'    outa[A15]~ 'low                          
                      
                        andn    outa, ram_mask 'clear 
'    return data_in                       
                        'unlock ram so other cogs can use it
                        'wrlong  ram_release, hires_ram_lock_ptr
read_byte_ret           ret  'return to caller

'---- drawa byte of pixels ------------------------------------------------------------------------------
'  data &= $7F 'get rid of msb
'  x := (col * 7) '- 7
hires_pixel_sub         
                                   
'  p := (WIDTH * y) + x
                        
                        'new routine using lut to replace multiply
                        'rdlong would be more efficient here, but 
                        'there was a problem reading bytes since they weren't
                        'long aligned...
                        'start at first column of row y
                        
                        mov     hires_t1, hires_ymulwidth_ptr
                        shl     hires_ypos, #1
                        add     hires_t1, hires_ypos  
                        rdbyte  hires_ptr0, hires_t1 
                        add     hires_t1, #1
                        shl     hires_ptr0, #8
                        rdbyte  hires_t2, hires_t1 
                        or      hires_ptr0, hires_t2
                        
                        mov     hires_ptr3, hires_ptr0 'copy our pointer so we can modify ptr0
                     
'                        repeat 40 '40 columns/bytes per row
                        mov     hires_cntr4, #40
                        mov     hires_parity, #255
hires_draw_column

'                            data := read_byte(mem_loc)
'                            'the msb is ignored since it's the color grouping bit
'                            'the other bits are displayed opposite to where they appear
'                            'ie the lsb bit appears on the left and each subsequent bit moves to the right.
'                            'read Apple II Computer Graphics page 70ish for more details.
'                            R2.Pixel (data, col, row)     
                        
                        'test carry bit (bit 7), set c flag
                        'and     hires_val, hires_bit7 wc, nr  'this will help determine which lut value to access based off previous byte
                        'mov     hires_val2, hires_val
                        'test    hires_val, #64 wc           'save 7th bit to check next byte
                        'call routine to get data byte from ram. routine will write data to hires_val
                        mov     ram_address, mem_loc
                        call    #read_byte
                        mov     hires_val, ram_read

                        'and     hires_val, #127  'get rid of msb since we don't need color info
                        'mov     hires_val2, hires_val
                        
'  x := (p & 7)'find x position in byte
                        'mov     hires_ypos, hires_ptr0
                        'and     hires_ypos, #7
                        'mov     hires_t1, hires_ypos
                        
                        'patch for more accurate colors in full color mode
                        'test screen_mode jump to end of routine if monochrome
                        'get byte from appropriate LUT (odd, even1, even2)
                        cmp     hires_screen_mode, #0  wz       'check screen mode
        if_z            jmp     #hires_pixel_save               'if monochrome skip

                        xor     hires_parity, #255 wz      'toggle odd/even parity check
                        
        if_c_and_z      mov     hires_lut_ptr, hires_oddc_lut_ptr         'odd byte with bit carried from even
        if_c_and_nz     mov     hires_lut_ptr, hires_even_lut_ptr        'even byte with bit carried from odd              
        if_nc_and_z     mov     hires_lut_ptr, hires_odd_lut_ptr          'odd byte
        if_nc_and_nz    mov     hires_lut_ptr, hires_even_lut_ptr         'even byte                   
                        
                        test    hires_val, #64 wc           'save 7th bit to check next byte
                        add     hires_lut_ptr, hires_val  'find correct value
                        rdbyte  hires_val, hires_lut_ptr  'save modified byte
hires_pixel_save
'  p := @pixel_bfr + (p >> 3)
                        shr     hires_ptr0, #3
                        add     hires_ptr0, par
                        wrbyte  hires_val, hires_ptr0 'put val directly into buffer, no manipulation
                        'mov     hires_ptr1, hires_ptr0
                        'add     hires_ptr1, #1
'  data2 := data << (x)
                        'shl     hires_val, hires_t1
                        'mov     hires_t2, hires_val
                       
'  mask := $FF000080 <- x
'  byte[p] &= mask
'  'write data to 1st byte
'  byte[p] |= data2
                        'rdbyte  hires_tmp, hires_ptr0
                        'start debug
                        'mov     debug_ptr, hires_tmp
                        'wrlong  debug_ptr, debug_val_ptr
                        'jmp     #hires_start  
                        'end debug
                        'mov     hires_tmp2, hires_t1
                        'mov     pixel_mask2, pixel_mask
                        'rol     pixel_mask2, hires_tmp2
                        'and     hires_tmp, pixel_mask2
                        'start debug
                        'mov     debug_ptr, hires_tmp
                        'wrlong  debug_ptr, debug_val_ptr
                        'jmp     #hires_start  
                        'end debug
                        'or      hires_tmp, hires_t2
                        'wrbyte  hires_tmp, hires_ptr0
                        
     
'  if x > 1
'    data2 := data >> (8 - x) 'data for right most byte
'    mask := $FF << (x - 1)
'    byte[p + 1] &= mask
'    byte[p + 1] |= data2
            '            mov     hires_t2, hires_t1
            '            shr     hires_t2, #1 wz
            '    if_z    jmp     #hires_pixel_next_col
            '    
            '            mov     hires_t2, #8
            '            sub     hires_t2, hires_t1
            '            shr     hires_val2, hires_t2
            '            
            '            rdbyte  hires_tmp, hires_ptr1
            '            sub     hires_t1, #1
            '            mov     hires_tmp2, #255
            '            shl     hires_tmp2, hires_t1
            '            and     hires_tmp, hires_tmp2
            '            or      hires_tmp, hires_val2
            '            wrbyte  hires_tmp, hires_ptr1 
                        
hires_pixel_next_col                       
                        add     hires_ptr3, #8 'add x
                        mov     hires_ptr0, hires_ptr3
'                            col++
                        'add     hires_col, #1    
'                            mem_loc++
                        add     mem_loc, #1
                        djnz    hires_cntr4, #hires_draw_column                    
'  if c byte[p] |= x
'  else byte[p] &= (!x)
'                        and     hires_val, #1  wz
'                        rdbyte  hires_tmp, hires_ptr0
'              if_nz     or      hires_tmp, hires_xpos
'              if_z      andn    hires_tmp, hires_xpos
'                        wrbyte  hires_tmp, hires_ptr0
hires_pixel_sub_ret     ret

hires_pixel             call    #hires_pixel_sub
                        jmp     #hires_cmd_start

hires_odd_lut_ptr       long    0
hires_even_lut_ptr      long    0
hires_oddc_lut_ptr      long    0
hires_evenc_lut_ptr     long    0
hires_blank_lut_ptr     long    0
hires_default_lut_ptr   long    0
hires_lut_ptr           long    0
hires_parity            long    0
hires_screen_mode_ptr   long    0
hires_screen_mode       long    0
hires_ymulwidth_ptr     long    0
draw_cmnd_ptr2          long    0
hires_cmnd_ptr          long    0
debug_ptr               long    0
debug_val_ptr           long    0
frame_cnt_hres_ptr      long    0
ss_page2_ptr            long    0
ss_mix_ptr              long    0
mode_retroii_ptr        long    0
pixel_mask              long    $FF_00_00_80
pixel_mask2             long    0
ram_we_mask             long    $40_00_00_00
ram_lsb_mask            long    $00_00_FF_00
ram_msb_mask            long    $0F_E0_00_00
ram_mask                long    $0F_E0_FF_00
ram_a15_mask            long    $80_00_00_00
ram_dira_mask           long    $8F_E0_FF_00
ram_address_test        long    $40_00
hires_page1             long    $20_00'$20_28 '$20_50 '$20_00
hires_page2             long    $40_00'$40_28 '$40_50 '$40_00
hires_row_start         long    0'0'64'128
mem_row_inc             long    $400
hires_busy_ptr          long    0
hires_is_busy           long    1
hires_not_busy          long    0
mem_box_mix             long    $200
mem_mix_start           long    $650
is_flashing             long    $FF
flash_counter           long    5
cog_num                 long    1
ram_release             long    0

text_type               res     1
mix_flashing            res     1
mix_inverse             res     1
hires_xpos              res     1
hires_ypos              res     1
hires_ptr0              res     1
hires_ptr1              res     1
hires_ptr2              res     1
hires_ptr3              res     1
hires_t1                res     1
hires_t2                res     1
hires_val               res     1
hires_val2              res     1
hires_tmp               res     1
hires_tmp2              res     1
hires_cntr2             res     1
hires_cntr3             res     1
hires_cntr4             res     1
hires_cntr              res     1
hires_cmnd              res     1
mem_loc                 res     1
mem_start               res     1
mem_page_start          res     1
ram_read                res     1
ram_address             res     1
ram_lsb                 res     1
ram_msb                 res     1
ram_a15                 res     1
hires_mem_box           res     1
hires_mem_row           res     1
hires_col               res     1
hires_row               res     1    

                        fit
DAT

ColorOdd
                        byte    $00
                        byte    $01
                        byte    $02
                        byte    $03
                        byte    $04
                        byte    $05
                        byte    $06
                        byte    $07
                        byte    $08
                        byte    $09
                        byte    $0A
                        byte    $0B
                        byte    $0C
                        byte    $0D
                        byte    $0E
                        byte    $0F
                        byte    $10
                        byte    $11
                        byte    $12
                        byte    $13
                        byte    $14
                        byte    $15
                        byte    $16
                        byte    $17
                        byte    $18
                        byte    $19
                        byte    $1A
                        byte    $1B
                        byte    $1C
                        byte    $1D
                        byte    $1E
                        byte    $1F
                        byte    $20
                        byte    $21
                        byte    $22
                        byte    $23
                        byte    $24
                        byte    $25
                        byte    $26
                        byte    $27
                        byte    $28
                        byte    $29
                        byte    $2A
                        byte    $2B
                        byte    $2C
                        byte    $2D
                        byte    $2E
                        byte    $2F
                        byte    $30
                        byte    $31
                        byte    $32
                        byte    $33
                        byte    $34
                        byte    $35
                        byte    $36
                        byte    $37
                        byte    $38
                        byte    $39
                        byte    $3A
                        byte    $3B
                        byte    $3C
                        byte    $3D
                        byte    $3E
                        byte    $3F
                        byte    $40
                        byte    $41
                        byte    $42
                        byte    $43
                        byte    $44
                        byte    $45
                        byte    $46
                        byte    $47
                        byte    $48
                        byte    $49
                        byte    $4A
                        byte    $4B
                        byte    $4C
                        byte    $4D
                        byte    $4E
                        byte    $4F
                        byte    $50
                        byte    $51
                        byte    $52
                        byte    $53
                        byte    $54
                        byte    $55
                        byte    $56
                        byte    $57
                        byte    $58
                        byte    $59
                        byte    $5A
                        byte    $5B
                        byte    $5C
                        byte    $5D
                        byte    $5E
                        byte    $5F
                        byte    $60
                        byte    $61
                        byte    $62
                        byte    $63
                        byte    $64
                        byte    $65
                        byte    $66
                        byte    $67
                        byte    $68
                        byte    $69
                        byte    $6A
                        byte    $6B
                        byte    $6C
                        byte    $6D
                        byte    $6E
                        byte    $6F
                        byte    $70
                        byte    $71
                        byte    $72
                        byte    $73
                        byte    $74
                        byte    $75
                        byte    $76
                        byte    $77
                        byte    $78
                        byte    $79
                        byte    $7A
                        byte    $7B
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
                        byte    $00
                        byte    $00
                        byte    $00
                        byte    $00
                        byte    $00
                        byte    $00
                        byte    $00
                        byte    $00
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
